neo-internalforce/ATX5Vbooster/Pictures/IMG_20260929_165536646.jpg

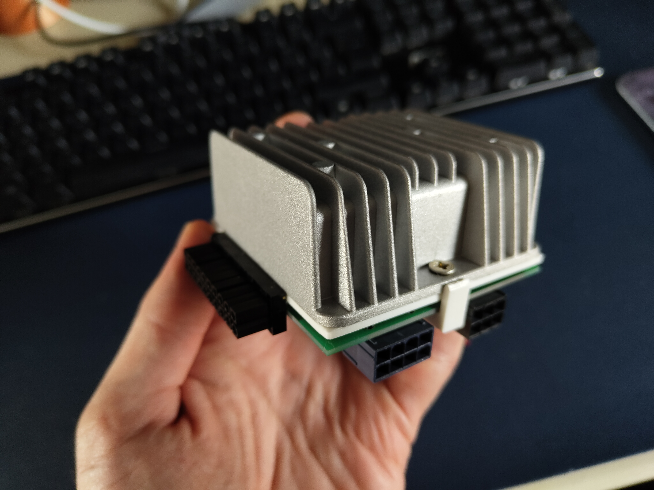
Pictures/IMG_20260929_165536646.jpg
