neo-internalforce/ATX5Vbooster/Pictures/IMG_20260929_110144453.jpg

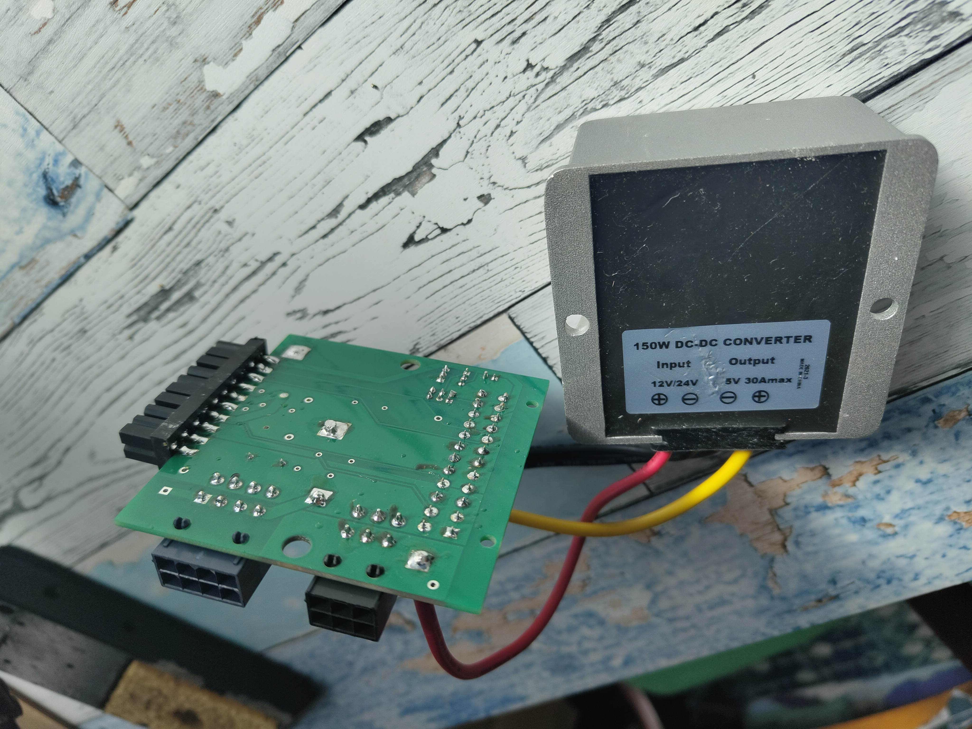
Pictures/IMG_20260929_110144453.jpg
